Marmota-Scientific/Simple-temperature-meter/Pictures/IMG00002.JPG

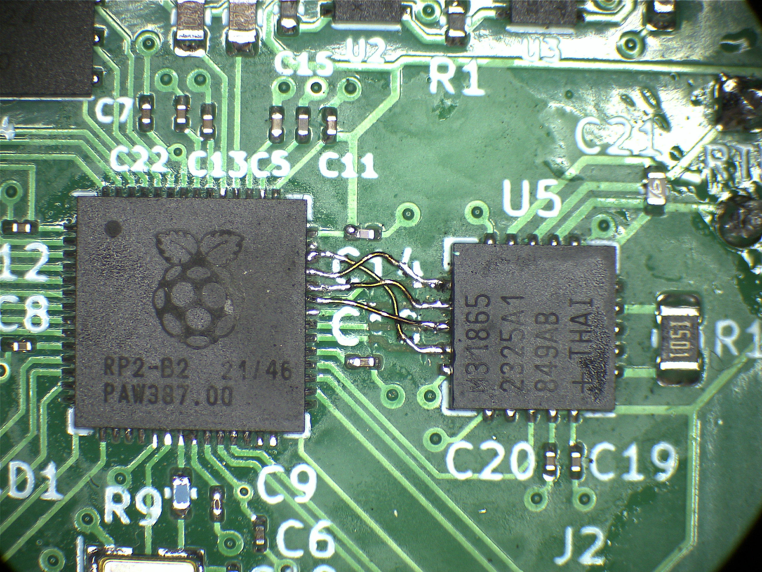
Pictures/IMG00002.JPG
